JohnMcWhirter10/ULSWAP-DAQ/ULSWAP-DAQ-1.0/doxygen/html/device_8h__incl.png

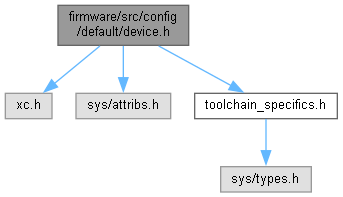
ULSWAP-DAQ-1.0/doxygen/html/device_8h__incl.png
