JohnMcWhirter10/ULSWAP-DAQ/ULSWAP-DAQ-1.0/doxygen/html/dir_3fea31fefb2c9a550fdfc646f25a1743_dep.png

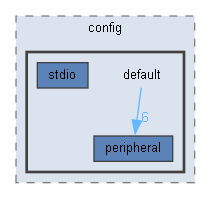
ULSWAP-DAQ-1.0/doxygen/html/dir_3fea31fefb2c9a550fdfc646f25a1743_dep.png
