JohnMcWhirter10/ULSWAP-DAQ/ULSWAP-DAQ-1.0/doxygen/html/dir_7fc79d37f1f5bd25c0c46cde9e52b1a1_dep.png

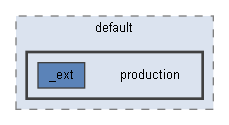
ULSWAP-DAQ-1.0/doxygen/html/dir_7fc79d37f1f5bd25c0c46cde9e52b1a1_dep.png
