JohnMcWhirter10/ULSWAP-DAQ/ULSWAP-DAQ-1.0/doxygen/html/dir_9dfb4c5c17edb0cea9c7609e5e343b45_dep.png

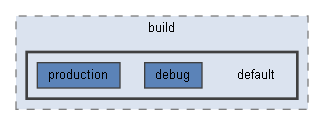
ULSWAP-DAQ-1.0/doxygen/html/dir_9dfb4c5c17edb0cea9c7609e5e343b45_dep.png
