JohnMcWhirter10/ULSWAP-DAQ/ULSWAP-DAQ-1.0/doxygen/html/dir_bb561306bc5168c0a13ad7a2338cc6d7_dep.png

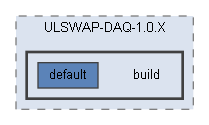
ULSWAP-DAQ-1.0/doxygen/html/dir_bb561306bc5168c0a13ad7a2338cc6d7_dep.png
