JohnMcWhirter10/ULSWAP-DAQ/ULSWAP-DAQ-1.0/doxygen/html/dir_c898ccd6027d5da3247aa855d21ca2cf_dep.png

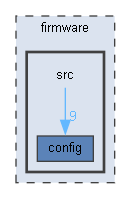
ULSWAP-DAQ-1.0/doxygen/html/dir_c898ccd6027d5da3247aa855d21ca2cf_dep.png
