JohnMcWhirter10/ULSWAP-DAQ/ULSWAP-DAQ-1.0/doxygen/html/dir_da0500e90e395e73238d74c4572ecf3c_dep.png

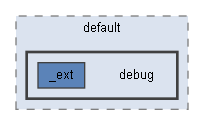
ULSWAP-DAQ-1.0/doxygen/html/dir_da0500e90e395e73238d74c4572ecf3c_dep.png
