JohnMcWhirter10/ULSWAP-DAQ/ULSWAP-DAQ-1.0/doxygen/html/dir_e36643b66d8ac04626ba01db246f4535_dep.png

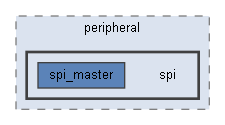
ULSWAP-DAQ-1.0/doxygen/html/dir_e36643b66d8ac04626ba01db246f4535_dep.png
