JohnMcWhirter10/ULSWAP-DAQ/ULSWAP-DAQ-1.0/doxygen/html/dir_e77302991068fc73f3ccf4f15242f482_dep.png

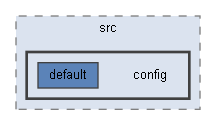
ULSWAP-DAQ-1.0/doxygen/html/dir_e77302991068fc73f3ccf4f15242f482_dep.png
