JohnMcWhirter10/ULSWAP-DAQ/ULSWAP-DAQ-1.0/doxygen/html/interrupts_8h__dep__incl.png

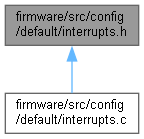
ULSWAP-DAQ-1.0/doxygen/html/interrupts_8h__dep__incl.png
