JohnMcWhirter10/ULSWAP-DAQ/ULSWAP-DAQ-1.0/doxygen/html/main_8c_a840291bc02cba5474a4cb46a9b9566fe_cgraph.png

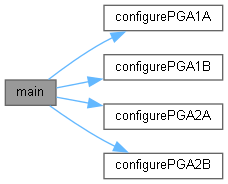
ULSWAP-DAQ-1.0/doxygen/html/main_8c_a840291bc02cba5474a4cb46a9b9566fe_cgraph.png
