JohnMcWhirter10/ULSWAP-DAQ/ULSWAP-DAQ-1.0/doxygen/html/plib__spi__master__common_8h__dep__incl.png

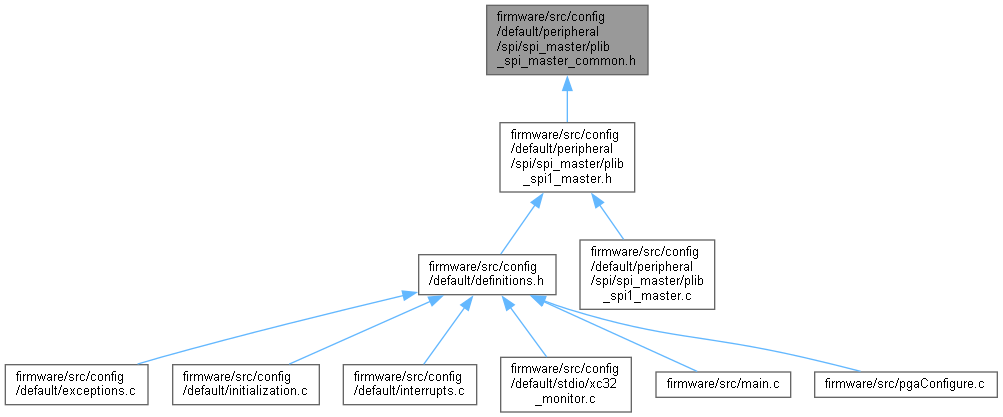
ULSWAP-DAQ-1.0/doxygen/html/plib__spi__master__common_8h__dep__incl.png
