JohnMcWhirter10/ULSWAP-DAQ/ULSWAP-DAQ-1.0/doxygen/html/plib__tmr__common_8h__incl.png

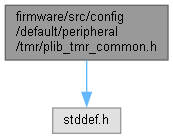
ULSWAP-DAQ-1.0/doxygen/html/plib__tmr__common_8h__incl.png
