JohnMcWhirter10/ULSWAP-DAQ/ULSWAP-DAQ-1.0/doxygen/html/plib__uart1_8c__incl.png

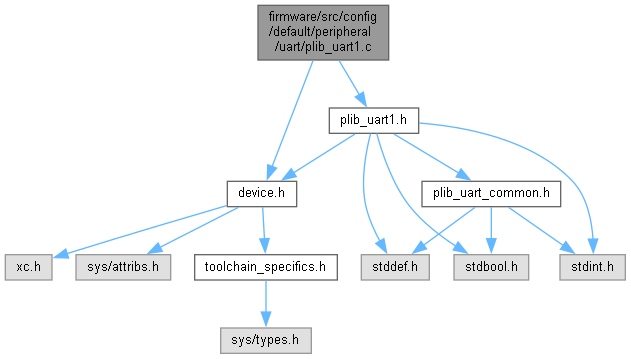
ULSWAP-DAQ-1.0/doxygen/html/plib__uart1_8c__incl.png
