JohnMcWhirter10/ULSWAP-DAQ/ULSWAP-DAQ-1.0/firmware/src/config/default/peripheral/uart/plib_uart1.c

/*******************************************************************************
  UART1 PLIB

  Company:
    Microchip Technology Inc.

  File Name:
    plib_uart1.c

  Summary:
    UART1 PLIB Implementation File

  Description:
    None

*******************************************************************************/

/*******************************************************************************
* Copyright (C) 2019 Microchip Technology Inc. and its subsidiaries.
*
* Subject to your compliance with these terms, you may use Microchip software
* and any derivatives exclusively with Microchip products. It is your
* responsibility to comply with third party license terms applicable to your
* use of third party software (including open source software) that may
* accompany Microchip software.
*
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
* IN NO EVENT WILL MICROCHIP BE LIABLE FOR ANY INDIRECT, SPECIAL, PUNITIVE,
* INCIDENTAL OR CONSEQUENTIAL LOSS, DAMAGE, COST OR EXPENSE OF ANY KIND
* WHATSOEVER RELATED TO THE SOFTWARE, HOWEVER CAUSED, EVEN IF MICROCHIP HAS
* BEEN ADVISED OF THE POSSIBILITY OR THE DAMAGES ARE FORESEEABLE. TO THE
* FULLEST EXTENT ALLOWED BY LAW, MICROCHIP'S TOTAL LIABILITY ON ALL CLAIMS IN
* ANY WAY RELATED TO THIS SOFTWARE WILL NOT EXCEED THE AMOUNT OF FEES, IF ANY,
* THAT YOU HAVE PAID DIRECTLY TO MICROCHIP FOR THIS SOFTWARE.
*******************************************************************************/

#include "device.h"
#include "plib_uart1.h"

// *****************************************************************************
// *****************************************************************************
// Section: UART1 Implementation
// *****************************************************************************
// *****************************************************************************


void static UART1_ErrorClear( void )
{
    UART_ERROR errors = UART_ERROR_NONE;
    uint8_t dummyData = 0u;

    errors = (UART_ERROR)(U1STA & (_U1STA_OERR_MASK | _U1STA_FERR_MASK | _U1STA_PERR_MASK));

    if(errors != UART_ERROR_NONE)
    {
        /* If it's a overrun error then clear it to flush FIFO */
        if(U1STA & _U1STA_OERR_MASK)
        {
            U1STACLR = _U1STA_OERR_MASK;
        }

        /* Read existing error bytes from FIFO to clear parity and framing error flags */
        while(U1STA & _U1STA_URXDA_MASK)
        {
            dummyData = U1RXREG;
        }

    }

    // Ignore the warning
    (void)dummyData;
}

void UART1_Initialize( void )
{
    /* Set up UxMODE bits */
    /* STSEL  = 0 */
    /* PDSEL = 0 */
    /* UEN = 0 */

    U1MODE = 0x0;

    /* Enable UART1 Receiver and Transmitter */
    U1STASET = (_U1STA_UTXEN_MASK | _U1STA_URXEN_MASK | _U1STA_UTXISEL1_MASK );

    /* BAUD Rate register Setup */
    U1BRG = 12;

    /* Turn ON UART1 */
    U1MODESET = _U1MODE_ON_MASK;
}

bool UART1_SerialSetup( UART_SERIAL_SETUP *setup, uint32_t srcClkFreq )
{
    bool status = false;
    uint32_t baud;
    uint32_t status_ctrl;
    bool brgh = 0;
    int32_t uxbrg = 0;

    if (setup != NULL)
    {
        baud = setup->baudRate;

        if ((baud == 0) || ((setup->dataWidth == UART_DATA_9_BIT) && (setup->parity != UART_PARITY_NONE)))
        {
            return status;
        }

        if(srcClkFreq == 0)
        {
            srcClkFreq = UART1_FrequencyGet();
        }

        /* Calculate BRG value */
        if (brgh == 0)
        {
            uxbrg = (((srcClkFreq >> 4) + (baud >> 1)) / baud ) - 1;
        }
        else
        {
            uxbrg = (((srcClkFreq >> 2) + (baud >> 1)) / baud ) - 1;
        }

        /* Check if the baud value can be set with low baud settings */
        if((uxbrg < 0) || (uxbrg > UINT16_MAX))
        {
            return status;
        }

        /* Turn OFF UART1. Save UTXEN, URXEN and UTXBRK bits as these are cleared upon disabling UART */

        status_ctrl = U1STA & (_U1STA_UTXEN_MASK | _U1STA_URXEN_MASK | _U1STA_UTXBRK_MASK);

        U1MODECLR = _U1MODE_ON_MASK;

        if(setup->dataWidth == UART_DATA_9_BIT)
        {
            /* Configure UART1 mode */
            U1MODE = (U1MODE & (~_U1MODE_PDSEL_MASK)) | setup->dataWidth;
        }
        else
        {
            /* Configure UART1 mode */
            U1MODE = (U1MODE & (~_U1MODE_PDSEL_MASK)) | setup->parity;
        }

        /* Configure UART1 mode */
        U1MODE = (U1MODE & (~_U1MODE_STSEL_MASK)) | setup->stopBits;

        /* Configure UART1 Baud Rate */
        U1BRG = uxbrg;

        U1MODESET = _U1MODE_ON_MASK;

        /* Re-enable UTXEN, URXEN and UTXBRK. */
        U1STASET = status_ctrl;

        status = true;
    }

    return status;
}

bool UART1_AutoBaudQuery( void )
{
    if(U1MODE & _U1MODE_ABAUD_MASK)
        return true;
    else
        return false;
}

void UART1_AutoBaudSet( bool enable )
{
    if( enable == true )
    {
        U1MODESET = _U1MODE_ABAUD_MASK;
    }

    /* Turning off ABAUD if it was on can lead to unpredictable behavior, so that
       direction of control is not allowed in this function.                      */
}

bool UART1_Read(void* buffer, const size_t size )
{
    bool status = false;
    uint8_t* lBuffer = (uint8_t* )buffer;
    uint32_t errorStatus = 0;
    size_t processedSize = 0;

    if(lBuffer != NULL)
    {
        /* Clear error flags and flush out error data that may have been received when no active request was pending */
        UART1_ErrorClear();

        while( size > processedSize )
        {
            while(!(U1STA & _U1STA_URXDA_MASK));

            /* Error status */
            errorStatus = (U1STA & (_U1STA_OERR_MASK | _U1STA_FERR_MASK | _U1STA_PERR_MASK));

            if(errorStatus != 0)
            {
                break;
            }
            if (( U1MODE & (_U1MODE_PDSEL0_MASK | _U1MODE_PDSEL1_MASK)) == (_U1MODE_PDSEL0_MASK | _U1MODE_PDSEL1_MASK))
            {
                /* 9-bit mode */
                *(uint16_t*)lBuffer = (U1RXREG );
                lBuffer += 2;
            }
            else
            {
                /* 8-bit mode */
                *lBuffer++ = (U1RXREG );
            }

            processedSize++;
        }

        if(size == processedSize)
        {
            status = true;
        }
    }

    return status;
}

bool UART1_Write( void* buffer, const size_t size )
{
    bool status = false;
    uint8_t* lBuffer = (uint8_t*)buffer;
    size_t processedSize = 0;

    if(lBuffer != NULL)
    {
        while( size > processedSize )
        {
            /* Wait while TX buffer is full */
            while (U1STA & _U1STA_UTXBF_MASK);

            if (( U1MODE & (_U1MODE_PDSEL0_MASK | _U1MODE_PDSEL1_MASK)) == (_U1MODE_PDSEL0_MASK | _U1MODE_PDSEL1_MASK))
            {
                /* 9-bit mode */
                U1TXREG = *(uint16_t*)lBuffer;
                lBuffer += 2;
            }
            else
            {
                /* 8-bit mode */
                U1TXREG = *lBuffer++;
            }

            processedSize++;
        }

        status = true;
    }

    return status;
}

UART_ERROR UART1_ErrorGet( void )
{
    UART_ERROR errors = UART_ERROR_NONE;

    errors = (UART_ERROR)(U1STA & (_U1STA_OERR_MASK | _U1STA_FERR_MASK | _U1STA_PERR_MASK));

    if(errors != UART_ERROR_NONE)
    {
        UART1_ErrorClear();
    }

    /* All errors are cleared, but send the previous error state */
    return errors;
}

void UART1_WriteByte(int data)
{
    while ((U1STA & _U1STA_UTXBF_MASK));

    U1TXREG = data;
}

bool UART1_TransmitterIsReady( void )
{
    bool status = false;

    if(!(U1STA & _U1STA_UTXBF_MASK))
    {
        status = true;
    }

    return status;
}

int UART1_ReadByte( void )
{
    return(U1RXREG);
}

bool UART1_ReceiverIsReady( void )
{
    bool status = false;

    if(_U1STA_URXDA_MASK == (U1STA & _U1STA_URXDA_MASK))
    {
        status = true;
    }

    return status;
}

bool UART1_TransmitComplete( void )
{
    bool transmitComplete = false;

    if((U1STA & _U1STA_TRMT_MASK))
    {
        transmitComplete = true;
    }

    return transmitComplete;
}
