JohnMcWhirter10/ULSWAP-DAQ/ULSWAP-DAQ-1.0/firmware/src/config/default/peripheral/uart/plib_uart_common.h

/*******************************************************************************
  UART PLIB

  Company:
    Microchip Technology Inc.

  File Name:
    plib_uart_common.h

  Summary:
    UART PLIB Common Header File

  Description:
    This file has prototype of all the interfaces which are common for all the
    UART peripherals.

*******************************************************************************/

/*******************************************************************************
* Copyright (C) 2019 Microchip Technology Inc. and its subsidiaries.
*
* Subject to your compliance with these terms, you may use Microchip software
* and any derivatives exclusively with Microchip products. It is your
* responsibility to comply with third party license terms applicable to your
* use of third party software (including open source software) that may
* accompany Microchip software.
*
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
* IN NO EVENT WILL MICROCHIP BE LIABLE FOR ANY INDIRECT, SPECIAL, PUNITIVE,
* INCIDENTAL OR CONSEQUENTIAL LOSS, DAMAGE, COST OR EXPENSE OF ANY KIND
* WHATSOEVER RELATED TO THE SOFTWARE, HOWEVER CAUSED, EVEN IF MICROCHIP HAS
* BEEN ADVISED OF THE POSSIBILITY OR THE DAMAGES ARE FORESEEABLE. TO THE
* FULLEST EXTENT ALLOWED BY LAW, MICROCHIP'S TOTAL LIABILITY ON ALL CLAIMS IN
* ANY WAY RELATED TO THIS SOFTWARE WILL NOT EXCEED THE AMOUNT OF FEES, IF ANY,
* THAT YOU HAVE PAID DIRECTLY TO MICROCHIP FOR THIS SOFTWARE.
*******************************************************************************/

#ifndef PLIB_UART_COMMON_H
#define PLIB_UART_COMMON_H

#include <stdint.h>
#include <stddef.h>
#include <stdbool.h>


/* Provide C++ Compatibility */
#ifdef __cplusplus

    extern "C" {

#endif

#define UART_RXFIFO_DEPTH       9

typedef enum
{
    UART_PARITY_NONE = 0x00,

    UART_PARITY_EVEN = 0x02,

    UART_PARITY_ODD =  0x04,

      /* Force the compiler to reserve 32-bit space for each enum */
    UART_PARITY_INVALID = 0xFFFFFFFF

} UART_PARITY;

typedef enum
{
    UART_DATA_8_BIT = 0x00,

    UART_DATA_9_BIT = 0x06,

    /* Force the compiler to reserve 32-bit memory for each enum */
    UART_DATA_INVALID = 0xFFFFFFFF

} UART_DATA;

typedef enum
{
    UART_STOP_1_BIT = 0x00,

    UART_STOP_2_BIT = 0x01,

    /* Force the compiler to reserve 32-bit memory for each enum */
    UART_STOP_INVALID = 0xFFFFFFFF

} UART_STOP;

typedef struct
{
    uint32_t baudRate;

    UART_PARITY parity;

    UART_DATA dataWidth;

    UART_STOP stopBits;

} UART_SERIAL_SETUP;

// *****************************************************************************
/* UART Errors
*/

typedef enum
{
    UART_ERROR_NONE = 0,
    UART_ERROR_OVERRUN = 0x00000002,
    UART_ERROR_FRAMING = 0x00000004,
    UART_ERROR_PARITY  = 0x00000008

} UART_ERROR;

typedef void (* UART_CALLBACK)( uintptr_t context );

// *****************************************************************************
// *****************************************************************************
// Section: Local: **** Do Not Use ****
// *****************************************************************************
// *****************************************************************************

typedef struct
{
    uint8_t *               txBuffer;
    size_t                  txSize;
    size_t                  txProcessedSize;
    UART_CALLBACK           txCallback;
    uintptr_t               txContext;
    bool                    txBusyStatus;

    uint8_t *               rxBuffer;
    size_t                  rxSize;
    size_t                  rxProcessedSize;
    UART_CALLBACK           rxCallback;
    uintptr_t               rxContext;
    bool                    rxBusyStatus;

    volatile UART_ERROR     errors;

} UART_OBJECT ;

typedef enum
{
    /* Threshold number of bytes are available in the receive ring buffer */
    UART_EVENT_READ_THRESHOLD_REACHED = 0,

    /* Receive ring buffer is full. Application must read the data out to avoid missing data on the next RX interrupt. */
    UART_EVENT_READ_BUFFER_FULL,

    /* USART error. Application must call the UARTx_ErrorGet API to get the type of error and clear the error. */
    UART_EVENT_READ_ERROR,

    /* Threshold number of free space is available in the transmit ring buffer */
    UART_EVENT_WRITE_THRESHOLD_REACHED,
}UART_EVENT;

typedef void (* UART_RING_BUFFER_CALLBACK)(UART_EVENT event, uintptr_t context );

// *****************************************************************************
// *****************************************************************************
// Section: Local: **** Do Not Use ****
// *****************************************************************************
// *****************************************************************************

typedef struct
{
    UART_RING_BUFFER_CALLBACK                           wrCallback;

    uintptr_t                                           wrContext;

    volatile uint32_t                                   wrInIndex;

    volatile uint32_t                                   wrOutIndex;

    bool                                                isWrNotificationEnabled;

    uint32_t                                            wrThreshold;

    uint32_t                                            wrBufferSize;

    bool                                                isWrNotifyPersistently;

    UART_RING_BUFFER_CALLBACK                           rdCallback;

    uintptr_t                                           rdContext;

    volatile uint32_t                                   rdInIndex;

    volatile uint32_t                                   rdOutIndex;

    uint32_t                                            rdBufferSize;

    bool                                                isRdNotificationEnabled;

    uint32_t                                            rdThreshold;

    bool                                                isRdNotifyPersistently;

    volatile UART_ERROR                                 errors;

} UART_RING_BUFFER_OBJECT;

/* Provide C++ Compatibility */
#ifdef __cplusplus

    }

#endif

#endif // PLIB_UART_COMMON_H
