JohnMcWhirter10/ULSWAP-DAQ/ULSWAP-DAQ-1.0/firmware/src/pgaConfigure.h

/* ************************************************************************** */
/** Descriptive File Name

  @Company
    Company Name

  @File Name
    filename.h

  @Summary
    Brief description of the file.

  @Description
    Describe the purpose of this file.
 */
/* ************************************************************************** */

void configurePGA1A(uint8_t config, uint8_t shdn);

void configurePGA1B(uint8_t config, uint8_t shdn);

void configurePGA2A(uint8_t config, uint8_t shdn);

void configurePGA2B(uint8_t config, uint8_t shdn);
